TrollingInDaDeep/DronesliderSwitches/images/backplate2.jpg

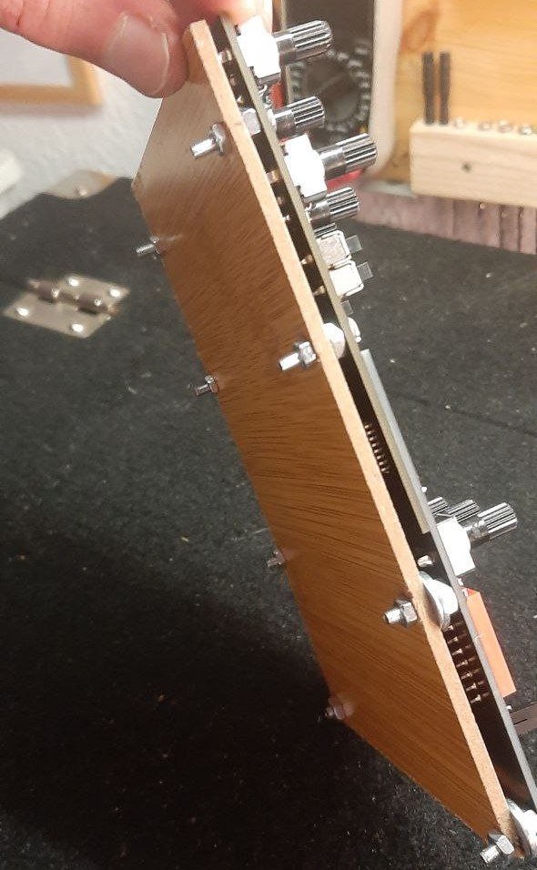
images/backplate2.jpg
